dword1511/stm32-tinyuwb/decartls/deca_range_tables.c

/*! ----------------------------------------------------------------------------
 *  @file    deca_range_tables.c
 *  @brief   DW1000 range correction tables
 *
 * @attention
 *
 * Copyright 2015 (c) DecaWave Ltd, Dublin, Ireland.
 *
 * All rights reserved.
 *
 */
#include <stdio.h>
#include <stdlib.h>

#include <decadriver/deca_device_api.h>
#include <decadriver/deca_param_types.h>

#define NUM_16M_OFFSET  (37)
#define NUM_16M_OFFSETWB  (68)
#define NUM_64M_OFFSET  (26)
#define NUM_64M_OFFSETWB  (59)

const uint8 chan_idxnb[NUM_CH_SUPPORTED] = {0, 0, 1, 2, 0, 3, 0, 0}; //only channels 1,2,3 and 5 are in the narrow band tables
const uint8 chan_idxwb[NUM_CH_SUPPORTED] = {0, 0, 0, 0, 0, 0, 0, 1}; //only channels 4 and 7 are in in the wide band tables

//---------------------------------------------------------------------------------------------------------------------------
// Range Bias Correction TABLES of range values in integer units of 25 CM, for 8-bit unsigned storage, MUST END IN 255 !!!!!!
//---------------------------------------------------------------------------------------------------------------------------

// offsets to nearest centimeter for index 0, all rest are +1 cm per value

#define CM_OFFSET_16M_NB    (-23)   // for normal band channels at 16 MHz PRF
#define CM_OFFSET_16M_WB    (-28)   // for wider  band channels at 16 MHz PRF
#define CM_OFFSET_64M_NB    (-17)   // for normal band channels at 64 MHz PRF
#define CM_OFFSET_64M_WB    (-30)   // for wider  band channels at 64 MHz PRF


//---------------------------------------------------------------------------------------------------------------------------
// range25cm16PRFnb: Range Bias Correction table for narrow band channels at 16 MHz PRF, NB: !!!! each MUST END IN 255 !!!!
//---------------------------------------------------------------------------------------------------------------------------

const uint8 range25cm16PRFnb[4][NUM_16M_OFFSET] =
{
    // ch 1 - range25cm16PRFnb
    {
           1,
           3,
           4,
           5,
           7,
           9,
          11,
          12,
          13,
          15,
          18,
          20,
          23,
          25,
          28,
          30,
          33,
          36,
          40,
          43,
          47,
          50,
          54,
          58,
          63,
          66,
          71,
          76,
          82,
          89,
          98,
         109,
         127,
         155,
         222,
         255,
         255
    },

    // ch 2 - range25cm16PRFnb
    {
           1,
           2,
           4,
           5,
           6,
           8,
           9,
          10,
          12,
          13,
          15,
          18,
          20,
          22,
          24,
          27,
          29,
          32,
          35,
          38,
          41,
          44,
          47,
          51,
          55,
          58,
          62,
          66,
          71,
          78,
          85,
          96,
         111,
         135,
         194,
         240,
         255
    },

    // ch 3 - range25cm16PRFnb
    {
           1,
           2,
           3,
           4,
           5,
           7,
           8,
           9,
          10,
          12,
          14,
          16,
          18,
          20,
          22,
          24,
          26,
          28,
          31,
          33,
          36,
          39,
          42,
          45,
          49,
          52,
          55,
          59,
          63,
          69,
          76,
          85,
          98,
         120,
         173,
         213,
         255
    },

    // ch 5 - range25cm16PRFnb
    {
           1,
           1,
           2,
           3,
           4,
           5,
           6,
           6,
           7,
           8,
           9,
          11,
          12,
          14,
          15,
          16,
          18,
          20,
          21,
          23,
          25,
          27,
          29,
          31,
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

    int rangeint25cm = (int) (range * 4.00) ;       // convert range to integer number of 25cm values.

    if (rangeint25cm > 255) rangeint25cm = 255 ;    // make sure it matches largest value in table (all tables end in 255 !!!!)

    if (prf == DWT_PRF_16M)
    {
        switch(chan)
        {
            case 4:
            case 7:
            {
                chanIdx = chan_idxwb[chan];
                while (rangeint25cm > range25cm16PRFwb[chanIdx][i]) i++ ;       // find index in table corresponding to range
                cmoffseti = i + CM_OFFSET_16M_WB ;                              // nearest centimeter correction
            }
            break;
            default:
            {
                chanIdx = chan_idxnb[chan];
                while (rangeint25cm > range25cm16PRFnb[chanIdx][i]) i++ ;       // find index in table corresponding to range
                cmoffseti = i + CM_OFFSET_16M_NB ;                              // nearest centimeter correction
            }
        }//end of switch
    }
    else // 64M PRF
    {
        switch(chan)
        {
            case 4:
            case 7:
            {
                chanIdx = chan_idxwb[chan];
                while (rangeint25cm > range25cm64PRFwb[chanIdx][i]) i++ ;       // find index in table corresponding to range
                cmoffseti = i + CM_OFFSET_64M_WB ;                              // nearest centimeter correction
            }
            break;
            default:
            {
                chanIdx = chan_idxnb[chan];
                while (rangeint25cm > range25cm64PRFnb[chanIdx][i]) i++ ;       // find index in table corresponding to range
                cmoffseti = i + CM_OFFSET_64M_NB ;                              // nearest centimeter correction
            }
        }//end of switch
    } // end else


    mOffset = (float) cmoffseti ;                                       // offset result in centimmetres

    mOffset *= 0.01 ;                                                   // convert to metres

    return (mOffset) ;
}
